mimnix/mimkb-83/assets/Layout.png

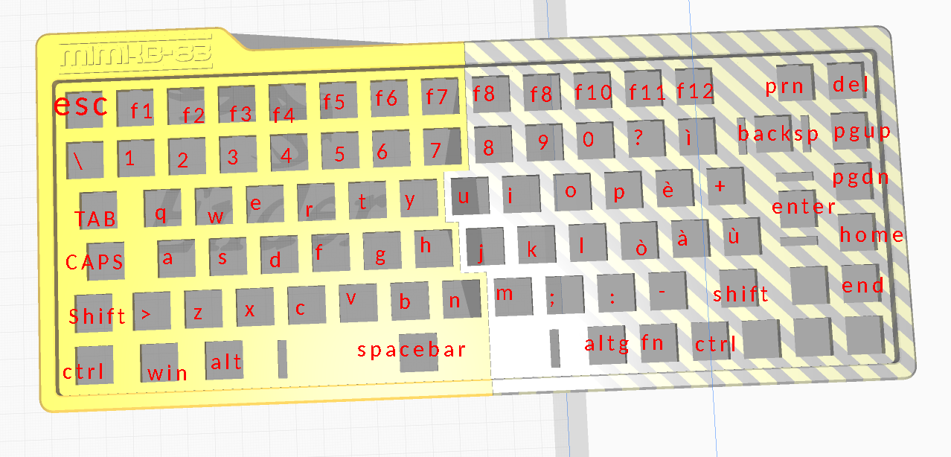
assets/Layout.png
