mimnix/mimkb-83/model/keycaps/STL/Keys Alt Fn Ctrl.stl

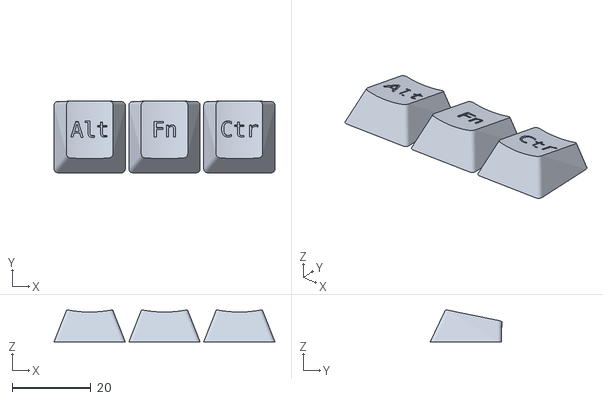
[picture p35: CAD file, 2022-10-11]
model/keycaps/STL/Keys Alt Fn Ctrl.stl
56.3 x 18.3 x 8.10
