mimnix/mimkb-83/model/keycaps/STL/Keys row2 1of2.stl

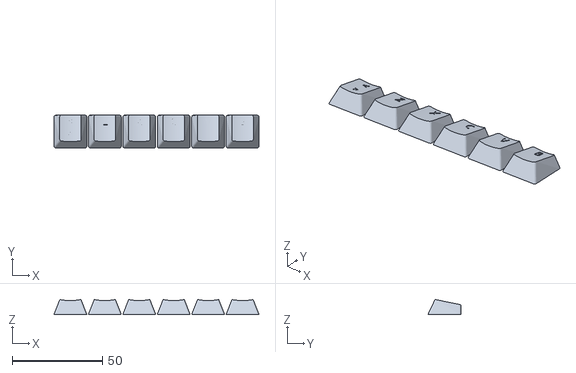
[picture p36: CAD file, 2022-10-11]
model/keycaps/STL/Keys row2 1of2.stl
113.4 x 18.3 x 8.10
