mimnix/mimkb-83/model/keycaps/STL/Keys row3 1of2.stl

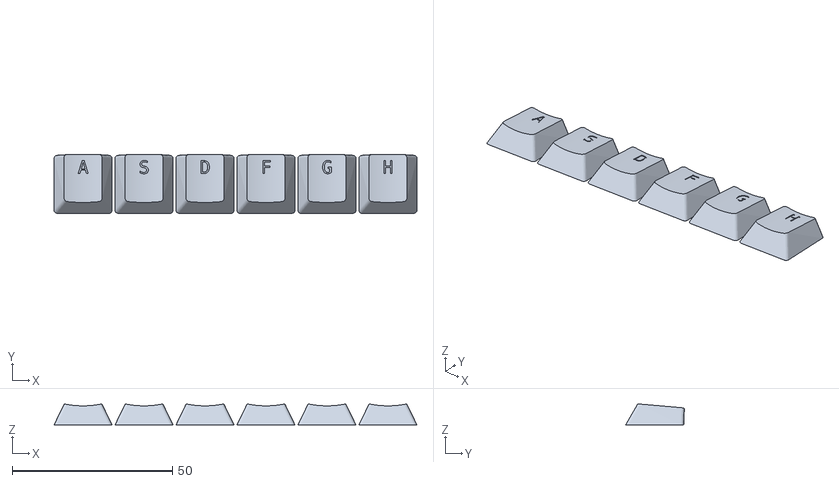
[picture p37: CAD file, 2022-10-11]
model/keycaps/STL/Keys row3 1of2.stl
113.4 x 18.4 x 6.52
