mimnix/mimkb-83/model/keycaps/STL/Keys Prn Del.stl

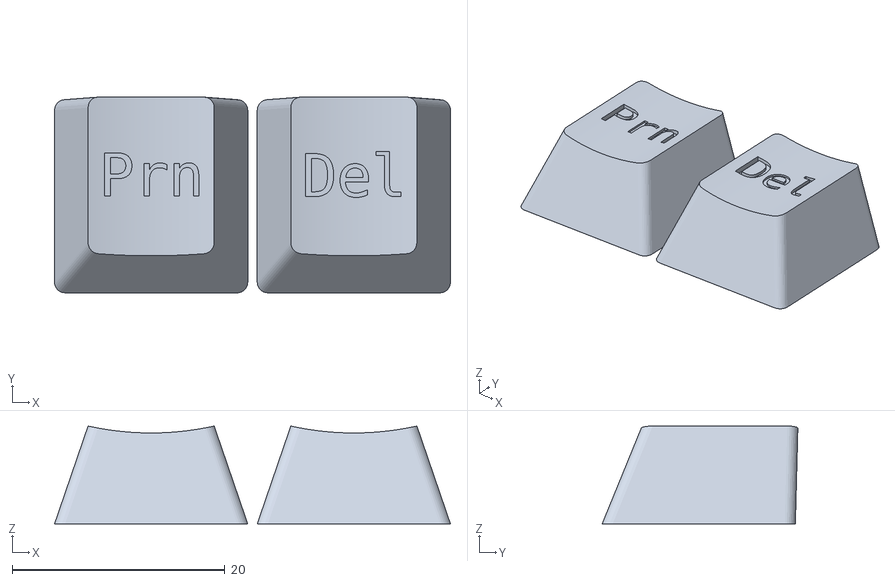
[picture p38: CAD file, 2022-10-11]
model/keycaps/STL/Keys Prn Del.stl
37.2 x 18.4 x 9.20
