mimnix/mimkb-83/model/keycaps/STL/Keys row5 1of2.stl

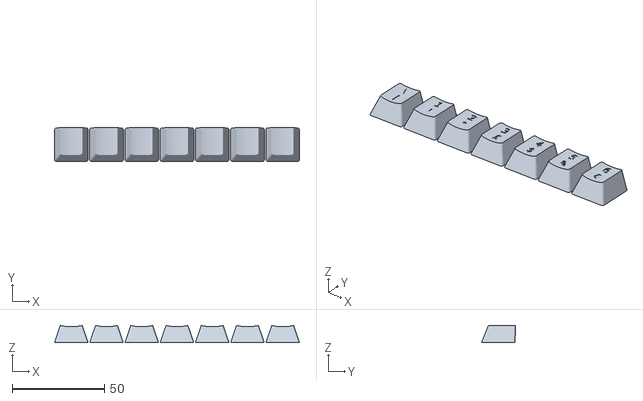
[picture p39: CAD file, 2022-10-11]
model/keycaps/STL/Keys row5 1of2.stl
132.5 x 18.4 x 9.20
