mimnix/mimkb-83/model/keycaps/STL/Keys row4 1of2.stl

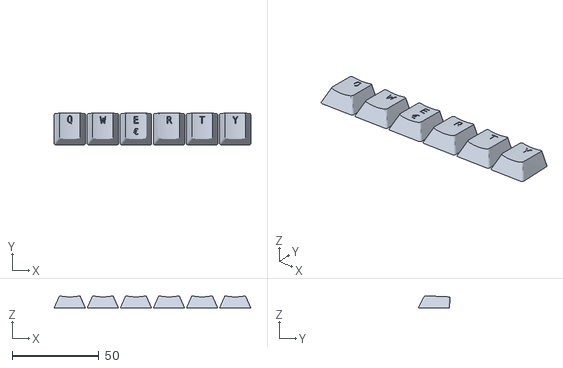
[picture p40: CAD file, 2022-10-11]
model/keycaps/STL/Keys row4 1of2.stl
113.4 x 18.4 x 7.13
