mimnix/mimkb-83/model/keycaps/STL/Keys Caps Home.stl

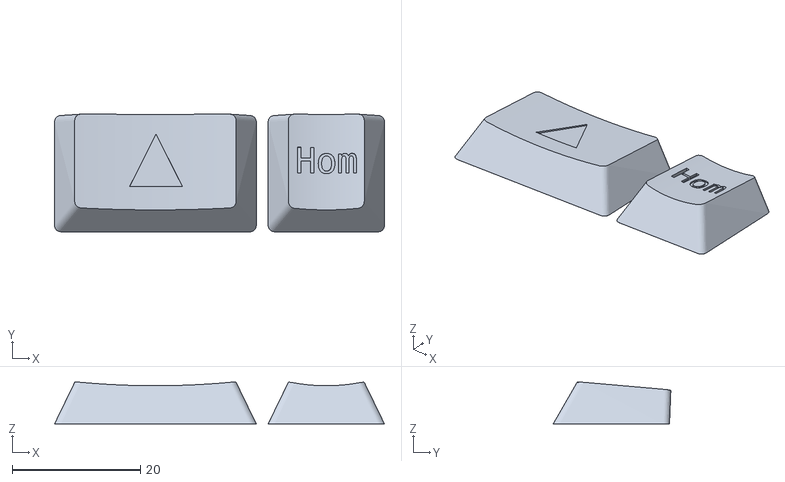
[picture p41: CAD file, 2022-10-11]
model/keycaps/STL/Keys Caps Home.stl
51.5 x 18.4 x 6.54
