mimnix/mimkb-83/model/keycaps/STL/Keys Ctrl Meta Alt.stl

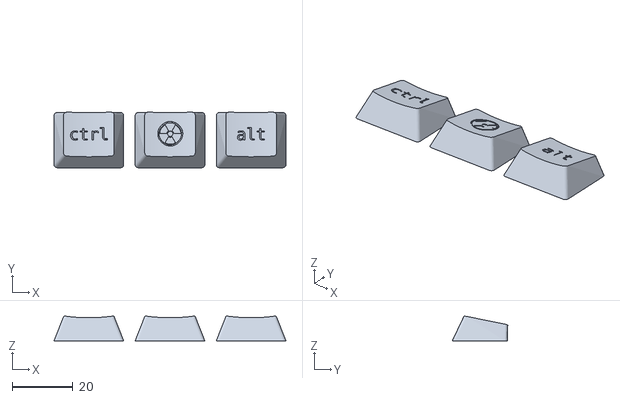
[picture p42: CAD file, 2022-10-11]
model/keycaps/STL/Keys Ctrl Meta Alt.stl
76.3 x 18.3 x 8.12
