mimnix/mimkb-83/model/keycaps/STL/Keys Esc.stl

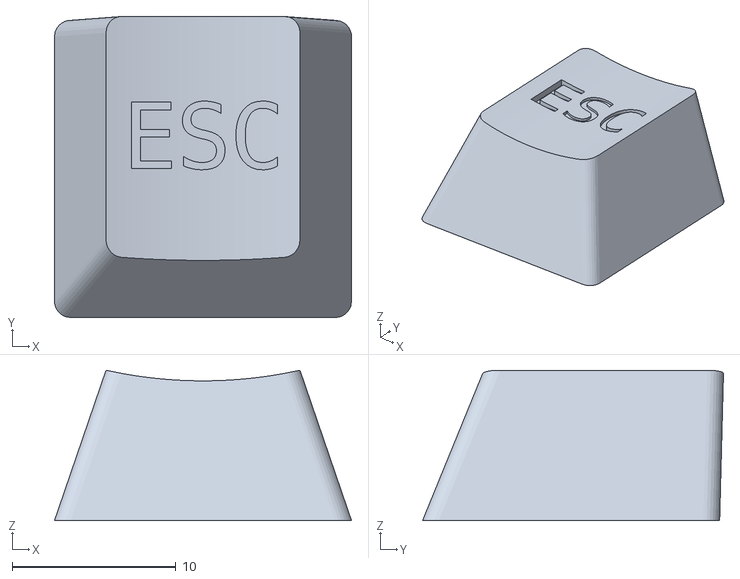
[picture p43: CAD file, 2022-10-11]
model/keycaps/STL/Keys Esc.stl
18.2 x 18.4 x 9.20
