mimnix/mimkb-83/model/keycaps/STL/Keys Tab PageDown.stl

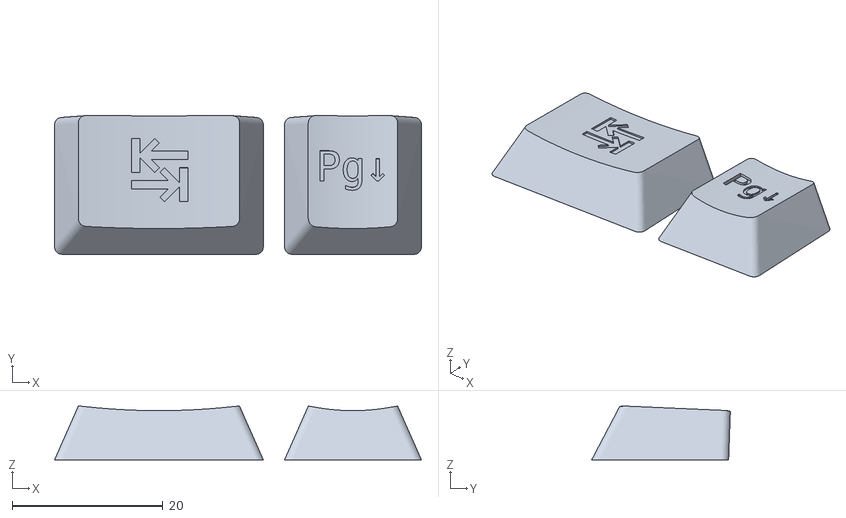
[picture p44: CAD file, 2022-10-11]
model/keycaps/STL/Keys Tab PageDown.stl
48.6 x 18.4 x 7.13
